wtarreau/power-switch/boards/pca9554d-v3/bottom-cream.png

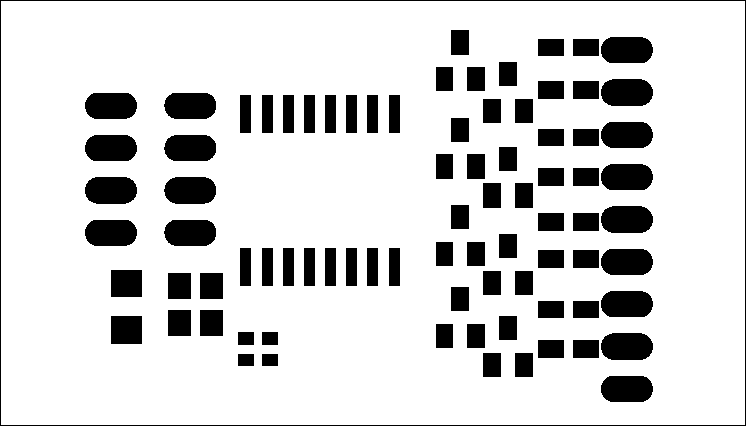
boards/pca9554d-v3/bottom-cream.png
